ThaatGuy/Sensation/Python/segnet_utils.py

import jetson.inference
import jetson.utils

import numpy as np


class segmentationBuffers:
    def __init__(self, net, args):
        self.net = net
        self.mask = None
        self.overlay = None
        self.composite = None
        self.class_mask = None
        
        self.use_stats = args.stats
        self.use_mask = "mask" in args.visualize
        self.use_overlay = "overlay" in args.visualize
        self.use_composite = self.use_mask and self.use_overlay
        
        if not self.use_overlay and not self.use_mask:
            raise Exception("invalid visualize flags - valid values are 'overlay' 'mask' 'overlay,mask'")
             
        self.grid_width, self.grid_height = net.GetGridSize()	
        self.num_classes = net.GetNumClasses()

    @property
    def output(self):
        if self.use_overlay and self.use_mask:
            return self.composite
        elif self.use_overlay:
            return self.overlay
        elif self.use_mask:
            return self.mask
            
    def Alloc(self, shape, format):
        if self.overlay is not None and self.overlay.height == shape[0] and self.overlay.width == shape[1]:
            return

        if self.use_overlay:
            self.overlay = jetson.utils.cudaAllocMapped(width=shape[1], height=shape[0], format=format)

        if self.use_mask:
            mask_downsample = 2 if self.use_overlay else 1
            self.mask = jetson.utils.cudaAllocMapped(width=shape[1]/mask_downsample, height=shape[0]/mask_downsample, format=format) 

        if self.use_composite:
            self.composite = jetson.utils.cudaAllocMapped(width=self.overlay.width+self.mask.width, height=self.overlay.height, format=format) 

        if self.use_stats:
            self.class_mask = jetson.utils.cudaAllocMapped(width=self.grid_width, height=self.grid_height, format="gray8")
            self.class_mask_np = jetson.utils.cudaToNumpy(self.class_mask)
            
    def ComputeStats(self):
        if not self.use_stats:
            return
            
        # get the class mask (each pixel contains the classID for that grid cell)
        self.net.Mask(self.class_mask, self.grid_width, self.grid_height)

        # compute the number of times each class occurs in the mask
        class_histogram, _ = np.histogram(self.class_mask_np, bins=self.num_classes, range=(0, self.num_classes-1))

        print('grid size:   {:d}x{:d}'.format(self.grid_width, self.grid_height))
        print('num classes: {:d}'.format(self.num_classes))

        print('-----------------------------------------')
        print(' ID  class name        count     %')
        print('-----------------------------------------')

        for n in range(self.num_classes):
            percentage = float(class_histogram[n]) / float(self.grid_width * self.grid_height)
            print(' {:>2d}  {:<18s} {:>3d}   {:f}'.format(n, self.net.GetClassDesc(n), class_histogram[n], percentage)) 
